MartinD-CZ/STM32F1-open-source-multimeter/case/case.JPG

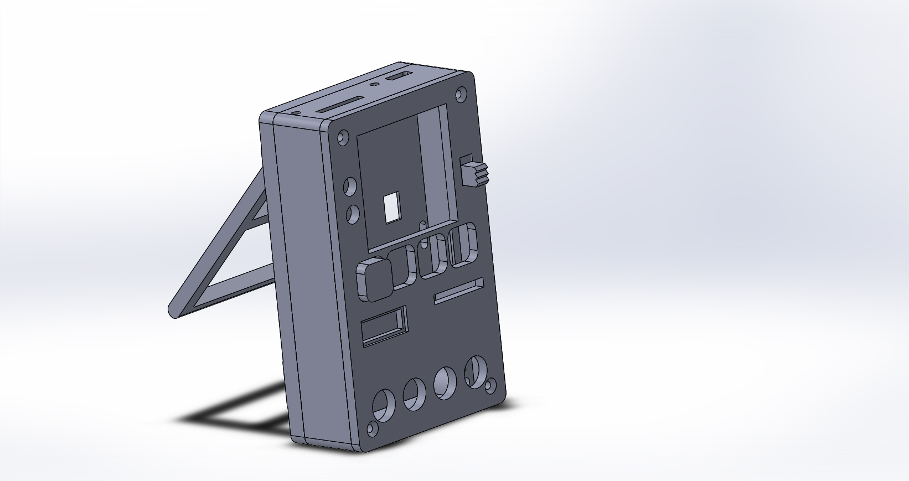
case/case.JPG
