MartinD-CZ/STM32F1-open-source-multimeter/firmware-multimeter/draw.h

#ifndef DRAW_H
#define DRAW_H

void drawSplashScreen(void);
void drawScreen(void);

void drawVoltScreen(void);
void drawCurrScreen(void);
void drawPowerScreen(void);
void drawContScreen(void);
void drawCompTestScreen(void);
void drawAboutScreen(void);
void drawFreqScreen(void);

#endif
